vladisenko/USB-CAN/photo/1.JPG

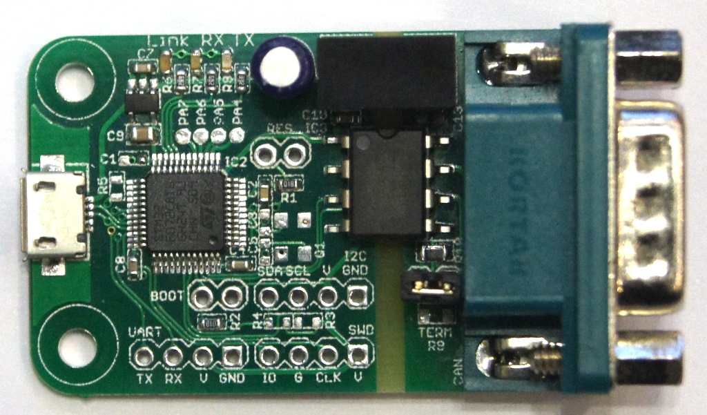
photo/1.JPG
